VictorGranado/Signal-Scanner/20251119_134031.jpg

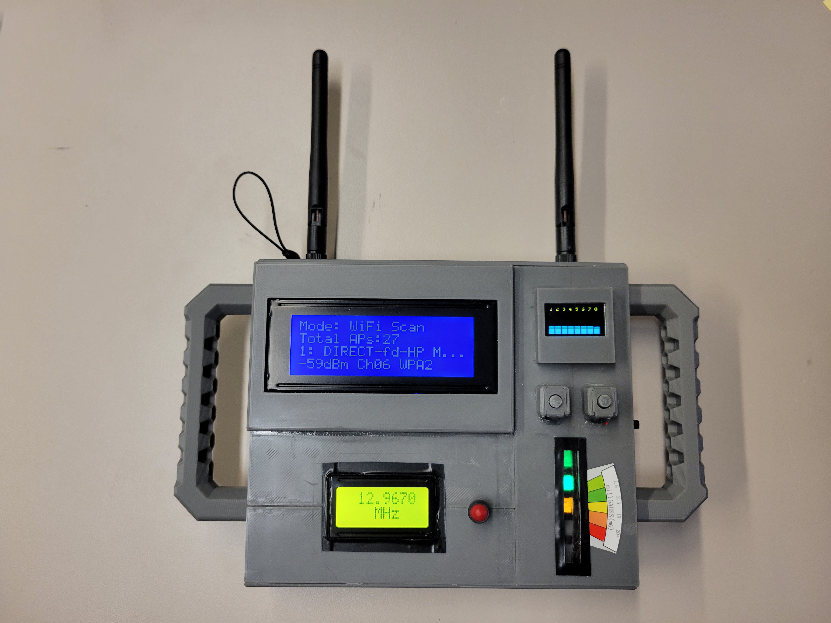
20251119_134031.jpg
