VictorGranado/Signal-Scanner/20251119_134133.jpg

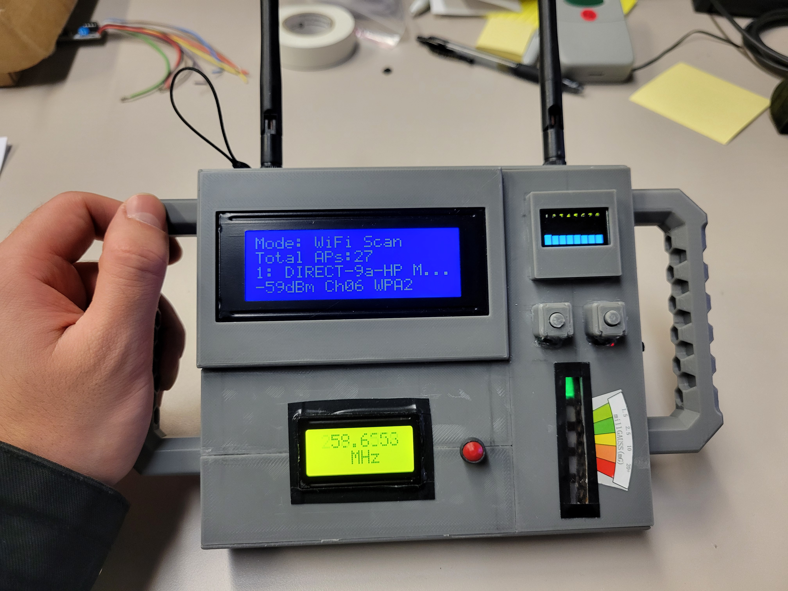
20251119_134133.jpg
