VictorGranado/Signal-Scanner/20251119_134144.jpg

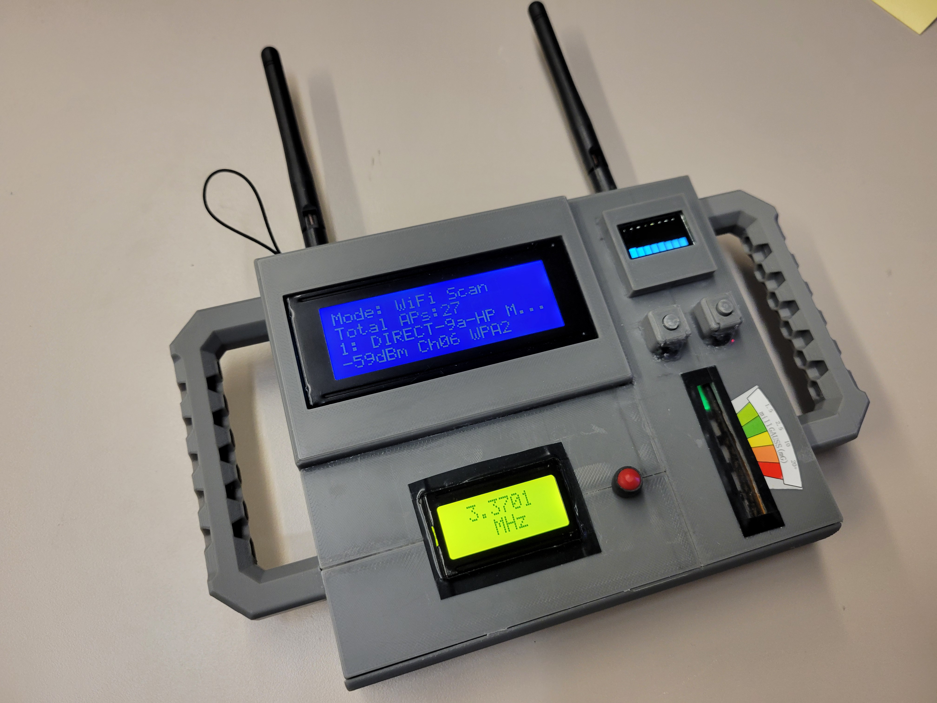
20251119_134144.jpg
